jsr606/CFO/original CFO/arduino/_CFO_IMAC_2011/Wavetables.pde

/*********************************************
 * Plays Sine Tone on Arduino Pocket Piano
 * Author: Owen Osborn, Copyright: GPL 
 * 
 *  This uses Direct Digital Synthesis (DDS)  for tone generation
 *   
 * 5 October 2007
 *
 * FOR MCP4921 DAC
 *
 * Chip type           : ATMEGA168
 * Clock frequency     : 16MHz
 *********************************************/
/* hacked up with lots of wavetables in progmem by Josh Brandt, 6 October 2008 */


#define SPI_SCK 5
#define SPI_MOSI 3


prog_uint8_t waveTable[] PROGMEM ={
// sine
  0x80,0x83,0x86,0x89,0x8c,0x8f,0x92,0x95,0x98,0x9c,0x9f,0xa2,0xa5,0xa8,0xab,0xae,
  0xb0,0xb3,0xb6,0xb9,0xbc,0xbf,0xc1,0xc4,0xc7,0xc9,0xcc,0xce,0xd1,0xd3,0xd5,0xd8,
  0xda,0xdc,0xde,0xe0,0xe2,0xe4,0xe6,0xe8,0xea,0xec,0xed,0xef,0xf0,0xf2,0xf3,0xf5,
  0xf6,0xf7,0xf8,0xf9,0xfa,0xfb,0xfc,0xfc,0xfd,0xfe,0xfe,0xff,0xff,0xff,0xff,0xff,
  0xff,0xff,0xff,0xff,0xff,0xff,0xfe,0xfe,0xfd,0xfc,0xfc,0xfb,0xfa,0xf9,0xf8,0xf7,
  0xf6,0xf5,0xf3,0xf2,0xf0,0xef,0xed,0xec,0xea,0xe8,0xe6,0xe4,0xe2,0xe0,0xde,0xdc,
  0xda,0xd8,0xd5,0xd3,0xd1,0xce,0xcc,0xc9,0xc7,0xc4,0xc1,0xbf,0xbc,0xb9,0xb6,0xb3,
  0xb0,0xae,0xab,0xa8,0xa5,0xa2,0x9f,0x9c,0x98,0x95,0x92,0x8f,0x8c,0x89,0x86,0x83,
  0x80,0x7c,0x79,0x76,0x73,0x70,0x6d,0x6a,0x67,0x63,0x60,0x5d,0x5a,0x57,0x54,0x51,
  0x4f,0x4c,0x49,0x46,0x43,0x40,0x3e,0x3b,0x38,0x36,0x33,0x31,0x2e,0x2c,0x2a,0x27,
  0x25,0x23,0x21,0x1f,0x1d,0x1b,0x19,0x17,0x15,0x13,0x12,0x10,0x0f,0x0d,0x0c,0x0a,
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
0x9b,0xb1,0x20,0xdd,0x74,0x06,0x18,0x0c,0x0f,0x2e,0x4c,0x66,0x7d,0x90,0xa1,0xaf,
0xbc,0xc6,0xcf,0xd7,0xde,0xe4,0xe9,0xed,0xf1,0xf4,0xf7,0xf9,0xfb,0xfc,0xfd,0xfd,
0xfd,0xfd,0xfd,0xfb,0xfa,0xf8,0xf6,0xf3,0xef,0xeb,0xe7,0xe1,0xdb,0xd3,0xcb,0xc1,
0xb6,0xa8,0x99,0x87,0x72,0x59,0x3d,0x1f,0x00,0x15,0x10,0x31,0xbe,0x74,0xdb,0x9b,
0x08,0x0f,0x07,0xca,0x3d,0x1f,0x34,0x26,0x0d,0x0d,0x25,0x3a,0x4c,0x5b,0x66,0x70,
0x78,0x7e,0x83,0x86,0x89,0x8b,0x8c,0x8d,0x8c,0x8c,0x8b,0x89,0x88,0x85,0x83,0x80,
0x7d,0x79,0x76,0x72,0x6d,0x68,0x63,0x5e,0x58,0x51,0x4a,0x42,0x39,0x30,0x25,0x19,
0x0c,0x03,0x14,0x29,0x40,0x5a,0x78,0x98,0xb6,0xc9,0xb9,0x62,0x26,0xa1,0x9e,0xba,
0x1b,0x20,0x4a,0x04,0x95,0xdb,0xe3,0xd1,0xb6,0x9b,0x82,0x6c,0x5a,0x4b,0x3e,0x33,
0x2a,0x23,0x1c,0x17,0x12,0x0e,0x0b,0x08,0x06,0x04,0x03,0x02,0x01,0x00,0x00,0x00,
0x00,0x00,0x00,0x01,0x02,0x04,0x05,0x07,0x0a,0x0d,0x10,0x14,0x19,0x1f,0x26,0x2e,
0x38,0x44,0x52,0x63,0x77,0x8e,0xa8,0xc4,0xdc,0xe4,0xc2,0x50,0x1c,0xdc,0x06,0x17,
0x87,0x6f,0x0b,0x18,0x99,0xc7,0xc2,0xa8,0x88,0x69,0x4d,0x34,0x1e,0x0b,0x04,0x13,
0x1f,0x2b,0x35,0x3e,0x46,0x4e,0x55,0x5b,0x61,0x66,0x6b,0x6f,0x74,0x78,0x7b,0x7f
};

// Here are variables for digital audio.  
// They are declared using normal AVR-GCC notation ('uint8_t' for unsigned 8 bit number)

// Here is the sine wave.  It is a one cycle of sine tone, 255 8 bit samples, in hex values
// you could put any wave form you line in here...

uint16_t sample;     // final sample that goes to the DAC    


// variables for carrier oscillator
uint16_t phaseAccumCarrier;
uint16_t phaseDeltaCarrier;
uint8_t indexCarrier;
uint8_t carrier;
uint8_t carrierAmp;

// variables for frequency mod oscillator
uint16_t phaseAccumModulator;
uint16_t phaseDeltaModulator;
uint8_t indexModulator;
int16_t modulatorSigned;
uint16_t modulator;
uint16_t modDepth;

// the two bytes that go to the DAC over SPI
uint8_t dacSPI0;
uint8_t dacSPI1;

// timer 2 is audio interrupt timer
ISR(TIMER2_COMPA_vect) {
  OCR2A = 127;
 
  PORTB &= ~(1<<2); // Frame sync low for SPI (making it low here so that we can measure lenght of interrupt with scope)

  phaseDeltaModulator = (frequency * harmonicity) >> 6;   // calculate modulator frequency for a  given harmonicity
  phaseDeltaCarrier = frequency;                          // this is just pitch (although not in Hz)

  // calculate frequency mod
  phaseAccumModulator = phaseAccumModulator + phaseDeltaModulator;
  indexModulator = phaseAccumModulator >> 8;
//  modulator = sineTable[indexModulator];
  
  memcpy_P(&modulator,&waveTable[modulatorWaveForm*256+indexModulator],1);
  modulator = (modulator * modulatorDepth) >> 3;
  modulatorSigned = modulator - ((128 * modulatorDepth) >> 3);   // center at 0

  // get carrier frequency
  phaseDeltaCarrier += modulatorSigned;

  // calculate carrier
  phaseAccumCarrier = phaseAccumCarrier + (phaseDeltaCarrier);
  indexCarrier = phaseAccumCarrier >> 8;
//  carrier = sineTable[indexCarrier];

  memcpy_P(&carrier,&waveTable[waveForm*256+indexCarrier],1);

  // output gain
  if (gateOn) {
    sample = carrier * gain;
  } else {
    sample = 0;
  }

  // format sample for SPI port
  dacSPI0 = sample >> 8;
  dacSPI0 >>= 4;
  dacSPI0 |= 0x30;
  dacSPI1 = sample >> 4;
  
  //Serial.print("M = ");
  //Serial.println(SPCR & (1 << MSTR), DEC);
  
  SPCR |= (1 << MSTR);

  //Serial.print("m = ");
  //Serial.println(SPCR & (1 << MSTR), DEC);
  

  // transmit value out the SPI port
  SPDR = dacSPI0;
  while (!(SPSR & (1<<SPIF)));
  SPDR = dacSPI1;
  while (!(SPSR & (1<<SPIF)));
  PORTB |= (1<<2); // Frame sync high
}
